moca0511/ESP32_UART_Bluetooth_Converter/pic/DSC_0401.JPG

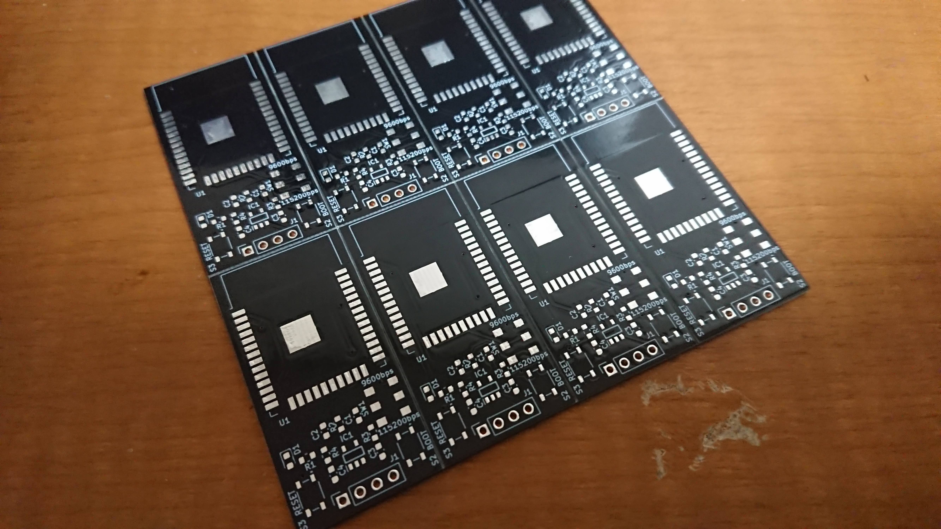
pic/DSC_0401.JPG
