moca0511/ESP32_UART_Bluetooth_Converter/pic/DSC_0402.JPG

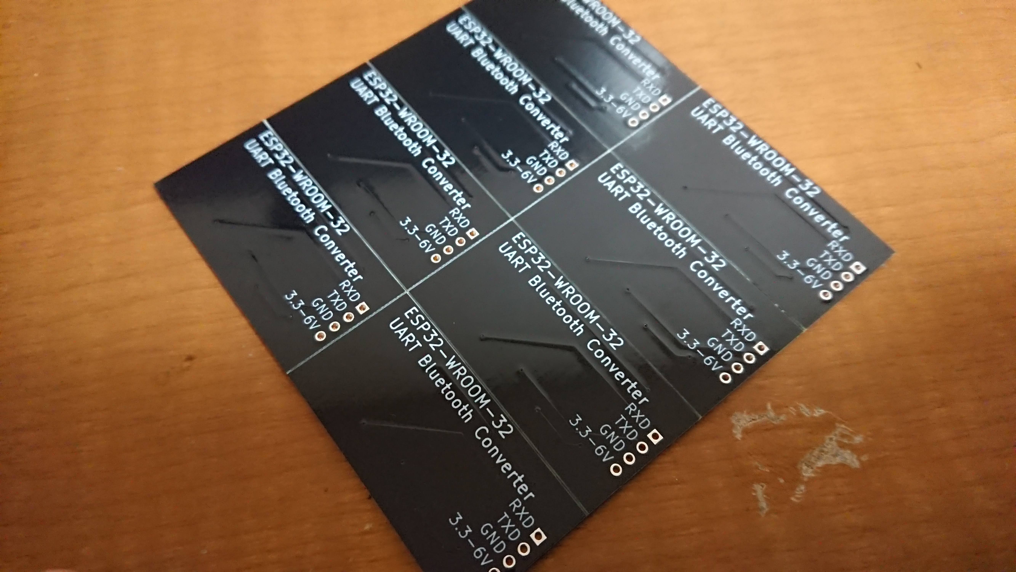
pic/DSC_0402.JPG
